federicogramos/deTmp11cic/manual/otherFiles/curva_fuerza.png

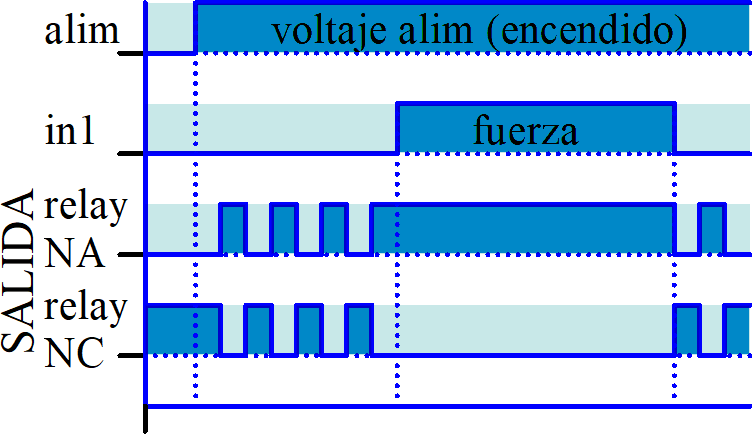
manual/otherFiles/curva_fuerza.png
