federicogramos/deTmp11cic/manual/otherFiles/curva_pause _off.png

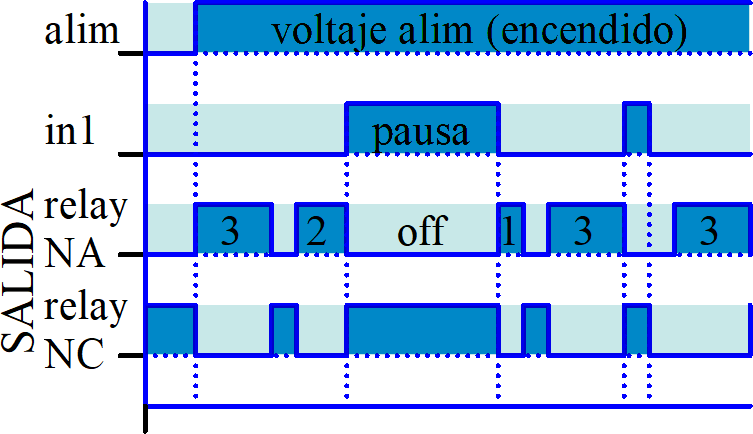
manual/otherFiles/curva_pause _off.png
