federicogramos/deTmp11cic/manual/otherFiles/curva_reset.png

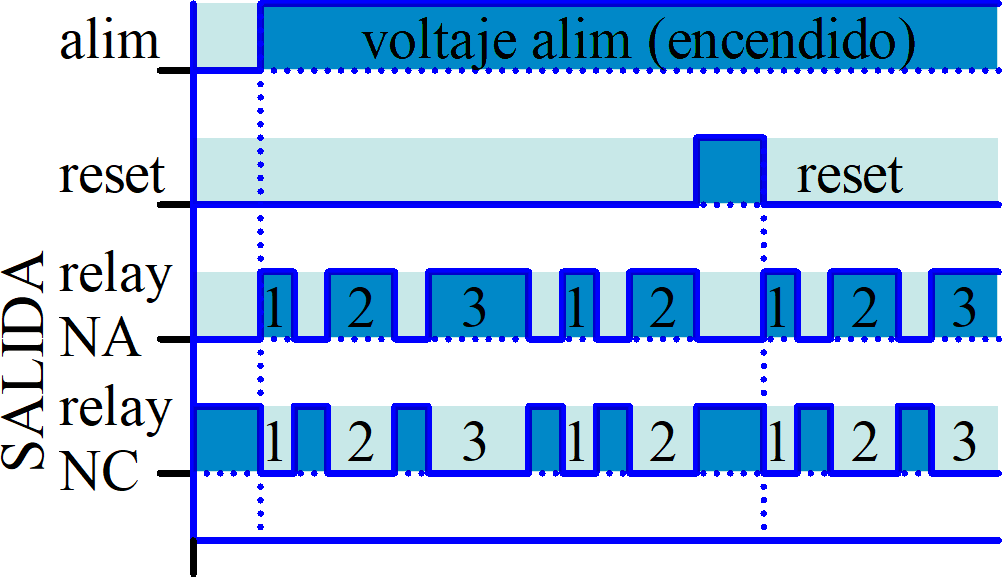
manual/otherFiles/curva_reset.png
