federicogramos/deTmp11cic/manual/otherFiles/diagrama_interior.png

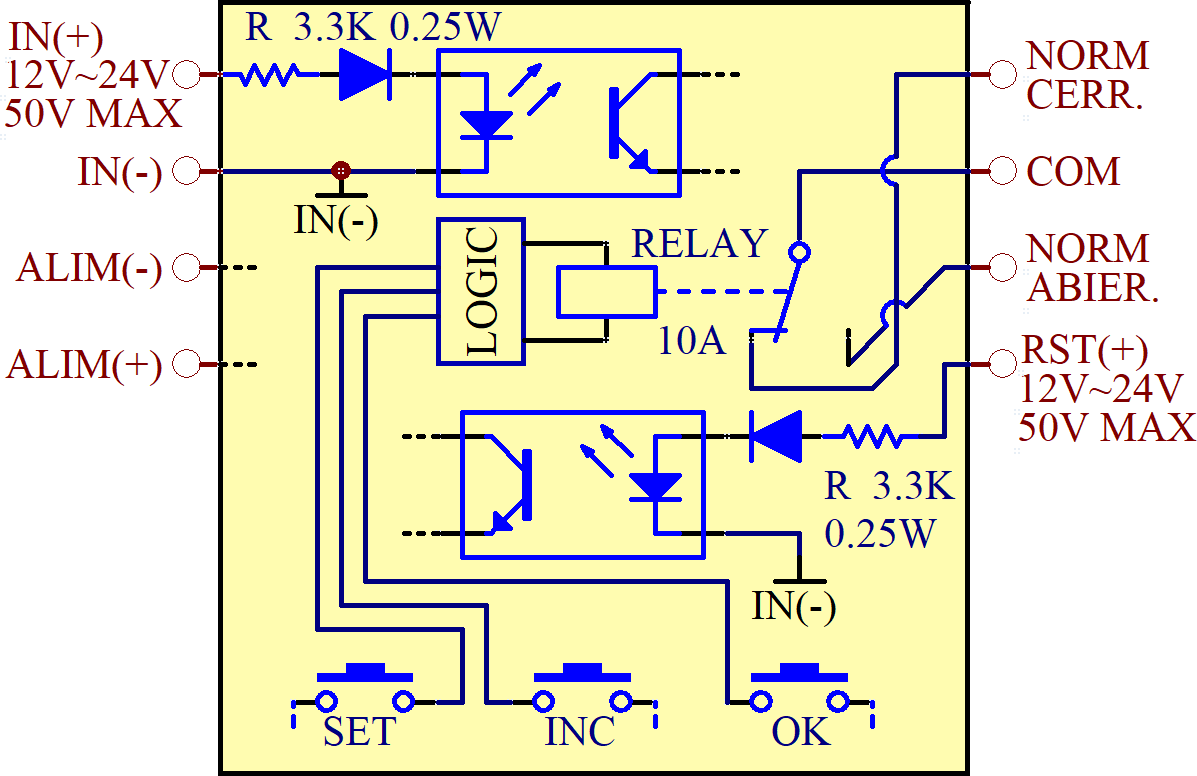
manual/otherFiles/diagrama_interior.png
