federicogramos/deTmp11cic/manual/otherFiles/ejemplo_carga_dc.png

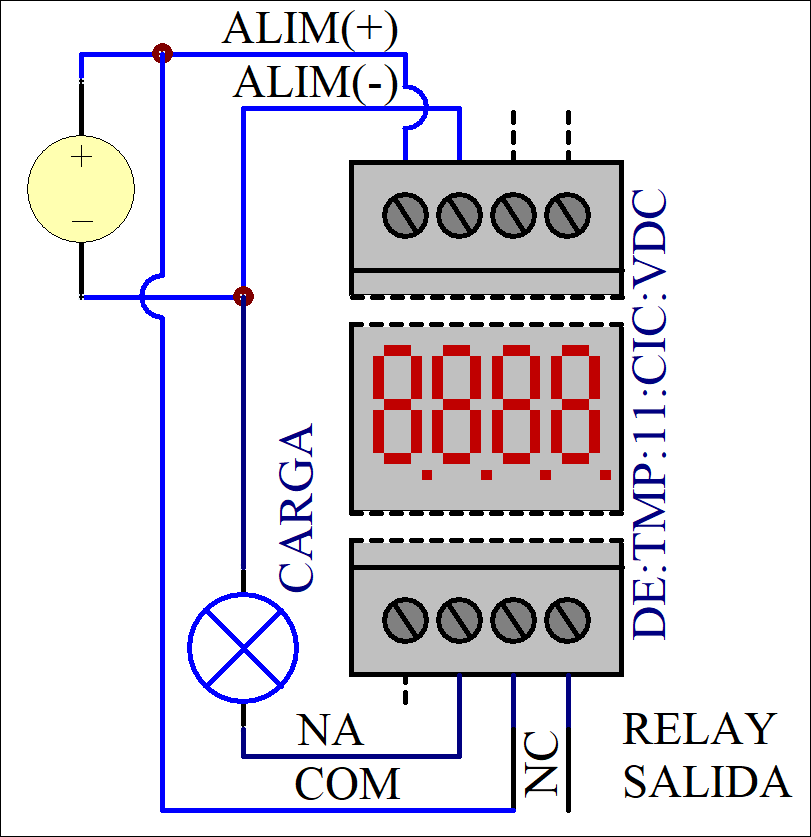
manual/otherFiles/ejemplo_carga_dc.png
