federicogramos/deTmp11cic/manual/otherFiles/ejemplo_misma_fuente.png

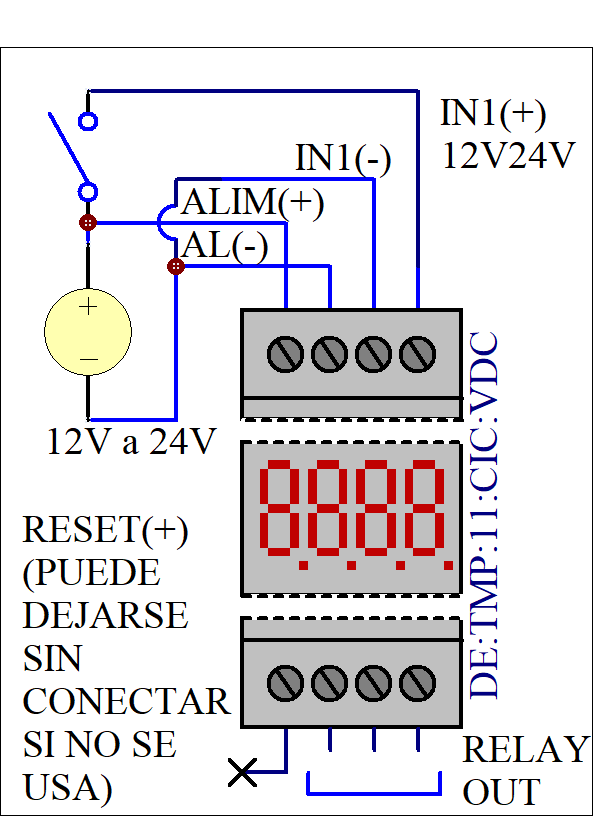
manual/otherFiles/ejemplo_misma_fuente.png
