federicogramos/deTmp11cic/manual/otherFiles/ejemplo_solenoide.png

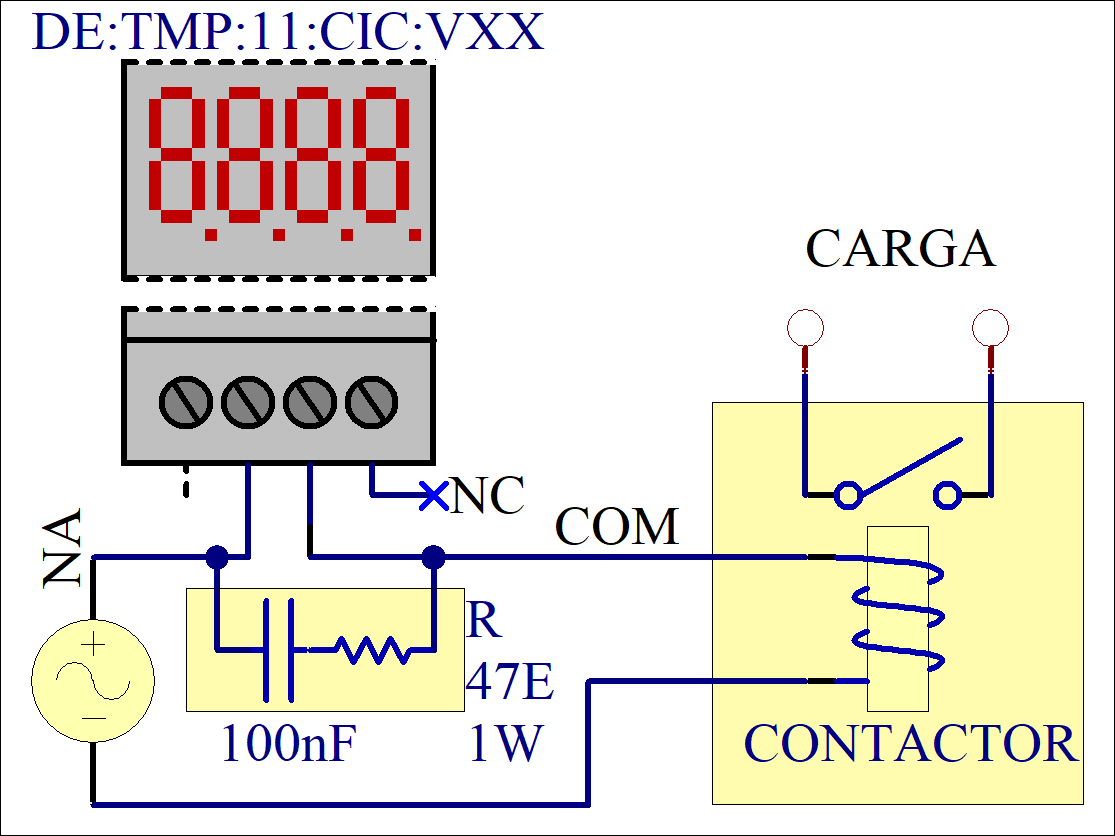
manual/otherFiles/ejemplo_solenoide.png
