federicogramos/deTmp11cic/manual/otherFiles/fisico_atras.png

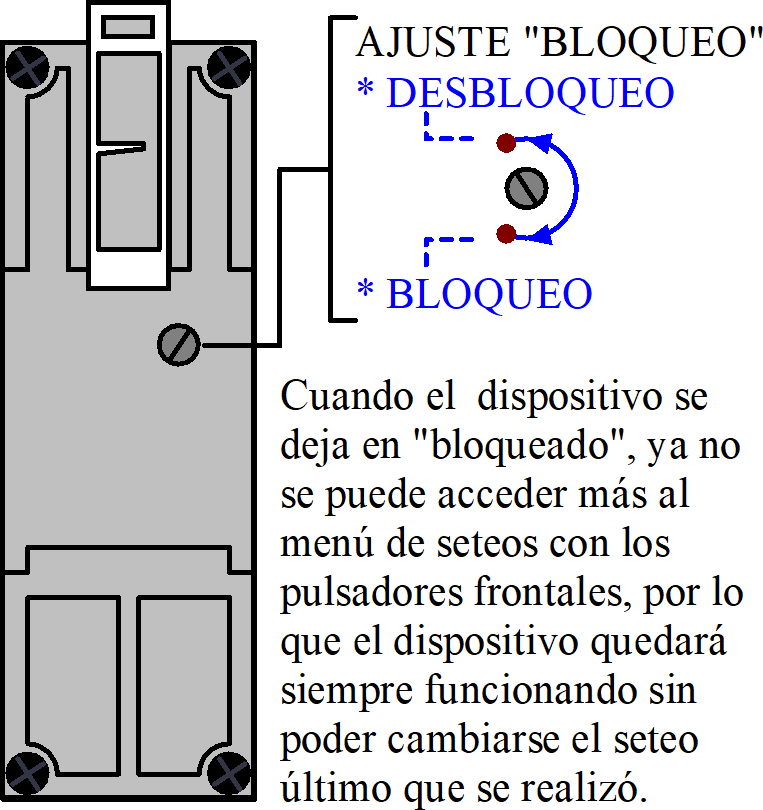
manual/otherFiles/fisico_atras.png
