federicogramos/deTmp11cic/manual/otherFiles/fisico_frente.png

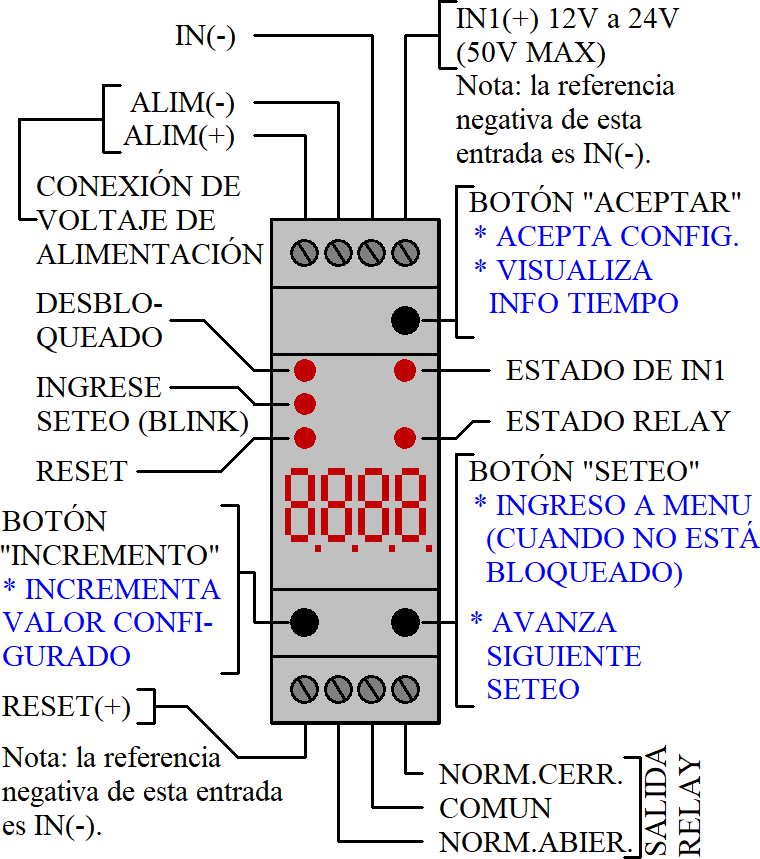
manual/otherFiles/fisico_frente.png
