federicogramos/deTmp11cic/manual/otherFiles/foto_preset_pcb.jpg

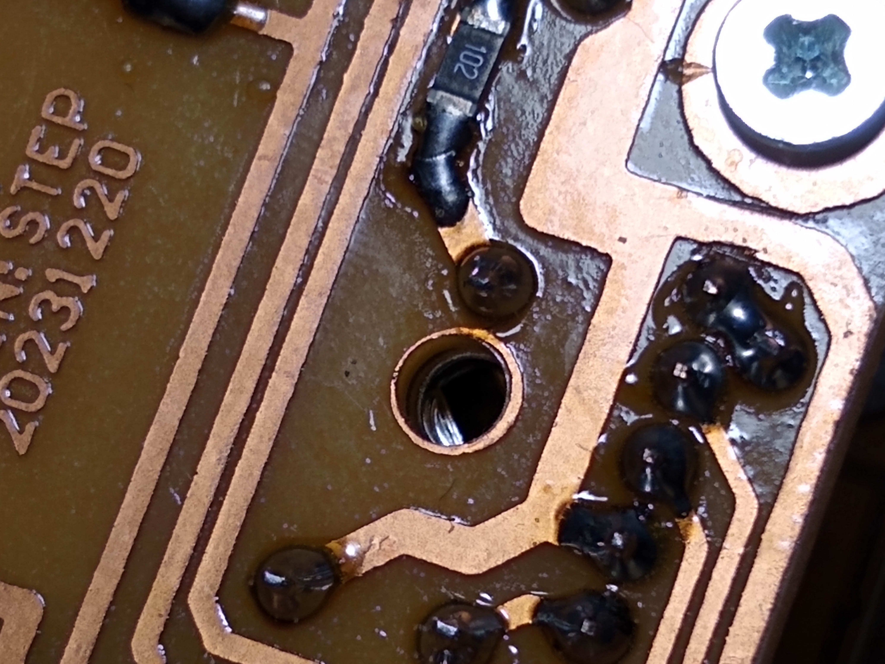
manual/otherFiles/foto_preset_pcb.jpg
