federicogramos/deTmp11cic/manual/otherFiles/gabinete.png

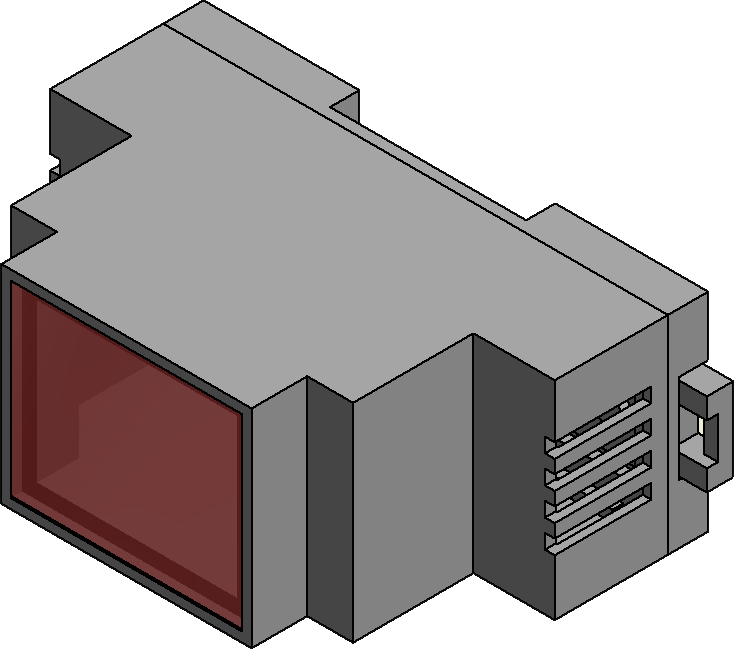
manual/otherFiles/gabinete.png
