federicogramos/deTmp11cic/manual/otherFiles/menu_pulsadores.png

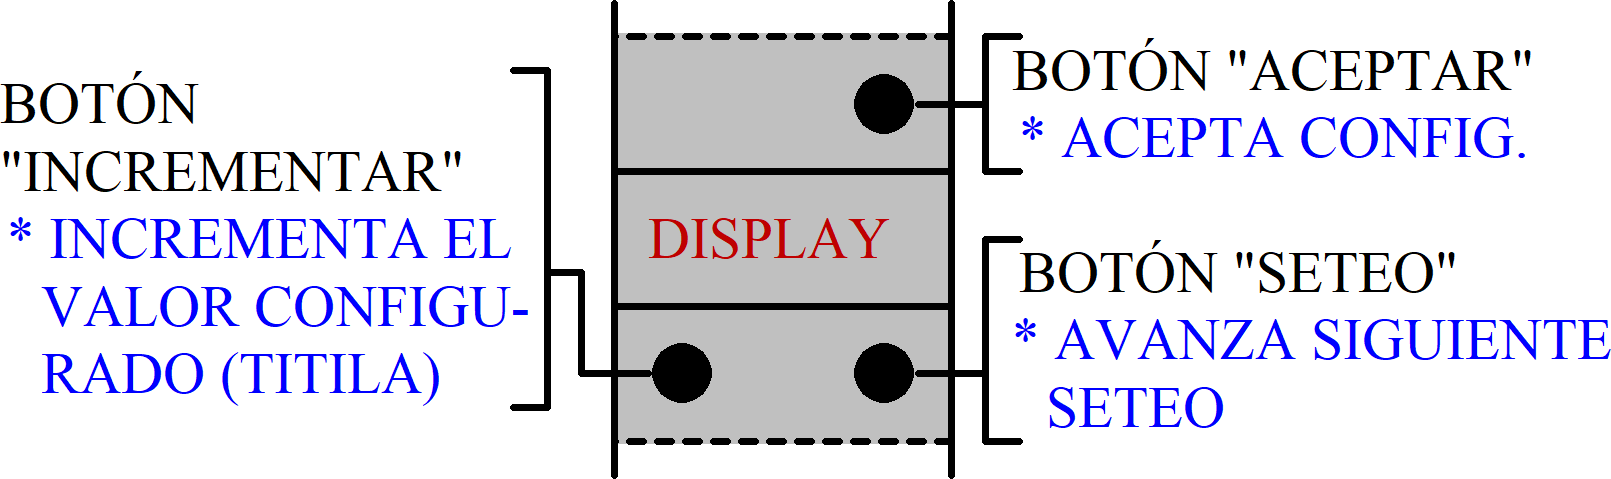
manual/otherFiles/menu_pulsadores.png
