federicogramos/deTmp11cic/sw/t0_aliases.h

//==============================================================================
// Archivo: t0_aliases.h
//==============================================================================


#ifndef __T0_ALIASES_H
#define __T0_ALIASES_H


//==============================================================================
// ALIAS
enum e_t0
    {
    T0_TESTDISPLAY,
    T0_MENU_RETURN,//TANTO DESDE MAIN MENU O CONFIGURACIONES ADICIONALES
    T0_PULSADO_LARGO_HOLD,
    T0_PULSADO_LARGO_SILENT,
    T0_D7SM_SCROLL,
    T0_CANT
    };
//==============================================================================


#endif//__T0_ALIASES_H
