federicogramos/deTmp11cic/sw/t0_setupUser.h

//==============================================================================
// Archivo: t0_setupUser.h
//==============================================================================


#ifndef __T0__SETUP_USER_H
#define __T0__SETUP_USER_H


//==============================================================================
// ALIAS
typedef unsigned char type_t0Size;//TAMAÑO DE VARIABLE QUE VA A CONTABILIZAR EL TIEMPO: char, int, long (unsigned or not)
typedef const type_t0Size type_t0DelayConstant;//SE GENERA UN ARRAY QUE CONTIENE LOS TIEMPOS DE DURACIÓN DE CADA TIMER. SE PUEDE DECLARAR "const" A ESTE TIPO DE DATO, PARA QUE NO OCUPE RAM EN CASO DE NO NECESITAR ALTERAR EL TIEMPO DE LOS TEMPORIZADORES.
//==============================================================================


#endif// __T0__SETUP_USER_H
