federicogramos/deTmp11cic/sw/t1_aliases.h

//==============================================================================
// Archivo: t1_aliases.h
//==============================================================================


#ifndef __T1_ALIASES_H
#define __T1_ALIASES_H


//==============================================================================
// ALIAS
enum e_t1
    {
    T1_TIME,
    T1_INTERMITENCIA_OUTPUT,
    T1_CANT
    };
//==============================================================================


#endif// __T1_ALIASES_H
