federicogramos/deTmp11cic/sw/t1_delays.h

//==============================================================================
// Archivo: t1_delays.h
//==============================================================================


#ifndef __T1_DELAYS_H
#define __T1_DELAYS_H


//==============================================================================
// DEFINICION DE TIEMPOS POR PARTE DEL USUARIO
//==============================================================================
type_t1DelayConstant t1DelayConstant[T1_CANT]=
    {
    0,
    0
    };
//==============================================================================


#endif// __T1_DELAYS_H
