federicogramos/deTmp11cic/sw/timerEeprom_aliases.h

//******************************************************************************
// ARCHIVO: timerEeprom_aliases.h
//******************************************************************************


#ifndef __TIMEREEPROM_ALIASES_H
#define __TIMEREEPROM_ALIASES_H


//******************************************************************************
// ALIAS
enum e_timerEeprom
    {
    TMREEPROM_TEST,
    CANT_TIMERS_EEPROM
    };

#endif//__TIMER_ALIASES_H
