federicogramos/deTmp11cic/sw/timerEeprom_delays.h

//******************************************************************************
// ARCHIVO: timerEeprom_delays.h
//******************************************************************************


#ifndef __TIMEREEPROM_DELAYS_H
#define __TIMEREEPROM_DELAYS_H


//******************************************************************************
// DEFINICION DE TIEMPOS POR PARTE DEL USUARIO
//******************************************************************************
type_timerEepromDelayConstant timerEepromDelayConstantAddress[CANT_TIMERS_EEPROM]=
    {
    0//TMR_TEST_DISPLAY=2s (base de tiempo timer=0.25s)
    };




#endif//__TIMER_DELAYS_H
